krocz/My_NixieClock/softwares/stm32/My_NixieClock/HARDWARE/MPU6050/mpuiic.h

#ifndef __MPUIIC_H
#define __MPUIIC_H
#include "sys.h"

//IO方向设置 PB7
#define MPU_SDA_IN()  {GPIOB->CRL&=0X0FFFFFFF;GPIOB->CRL|=(u32)8<<28;}  
#define MPU_SDA_OUT() {GPIOB->CRL&=0X0FFFFFFF;GPIOB->CRL|=(u32)3<<28;} 

//IO操作函数	 
#define MPU_IIC_SCL    PBout(6) 		//SCL
#define MPU_IIC_SDA    PBout(7) 		//SDA	 
#define MPU_READ_SDA   PBin(7) 		//输入SDA 

//IIC所有操作函数
void MPU_IIC_Delay(void);				//MPU IIC延时函数
void MPU_IIC_Init(void);                //初始化IIC的IO口				 
void MPU_IIC_Start(void);				//发送IIC开始信号
void MPU_IIC_Stop(void);	  			//发送IIC停止信号
void MPU_IIC_Send_Byte(u8 txd);			//IIC发送一个字节
u8 MPU_IIC_Read_Byte(unsigned char ack);//IIC读取一个字节
u8 MPU_IIC_Wait_Ack(void); 				//IIC等待ACK信号
void MPU_IIC_Ack(void);					//IIC发送ACK信号
void MPU_IIC_NAck(void);				//IIC不发送ACK信号

void IMPU_IC_Write_One_Byte(u8 daddr,u8 addr,u8 data);
u8 MPU_IIC_Read_One_Byte(u8 daddr,u8 addr);	  
#endif
